liana-keesing/Arduino-Anomaloscope/CAD/Base.png

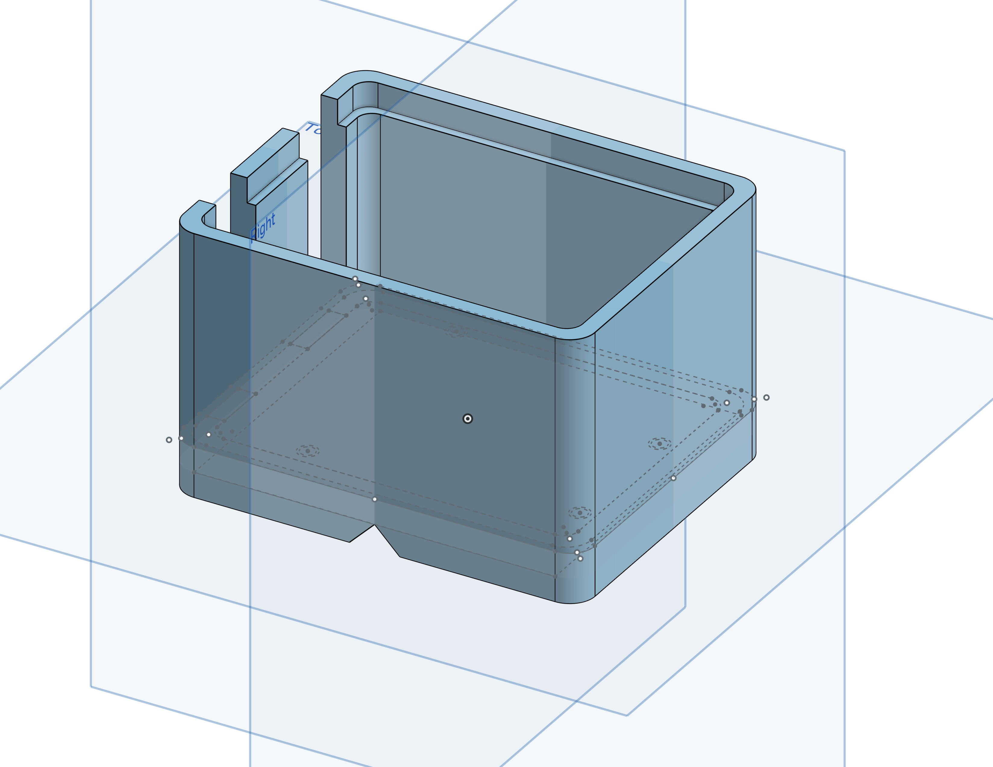
CAD/Base.png
