liana-keesing/Arduino-Anomaloscope/CAD/TopLayer.png

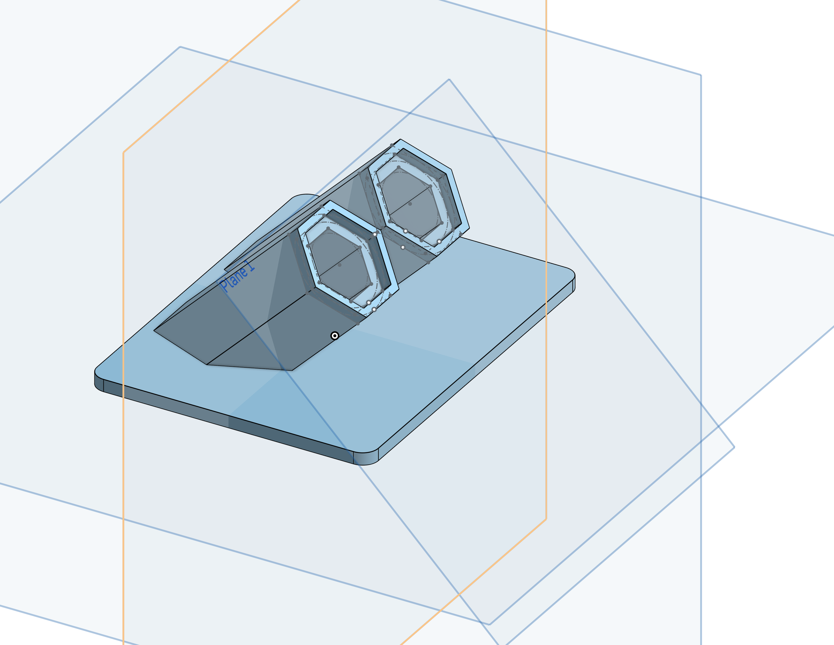
CAD/TopLayer.png
