liana-keesing/Arduino-Anomaloscope/CAD/Assembled1.png

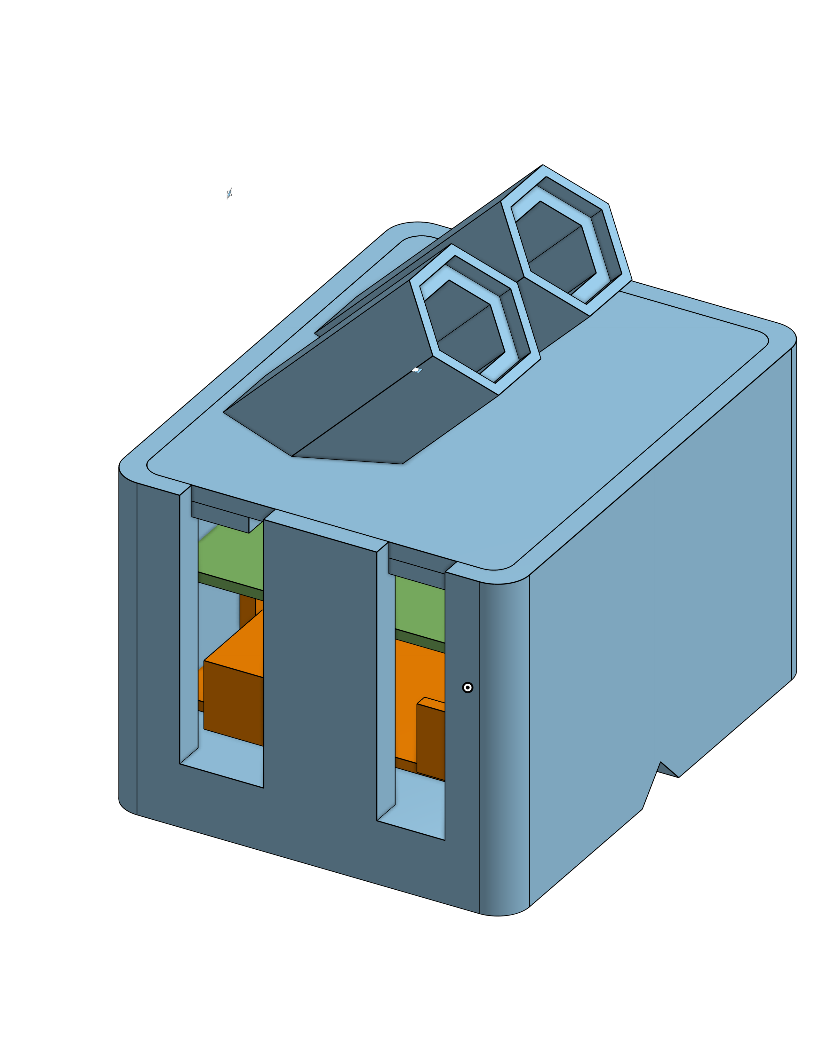
CAD/Assembled1.png
