liana-keesing/Arduino-Anomaloscope/CAD/Assembled2.png

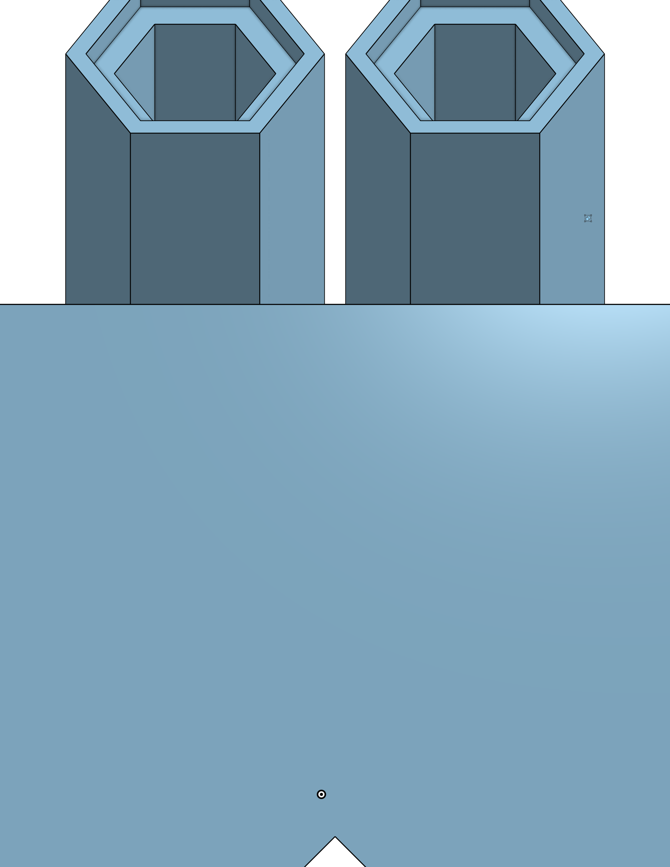
CAD/Assembled2.png
